talahuhta/PCB-Manufacturing-Project/pictures/3D2.jpg

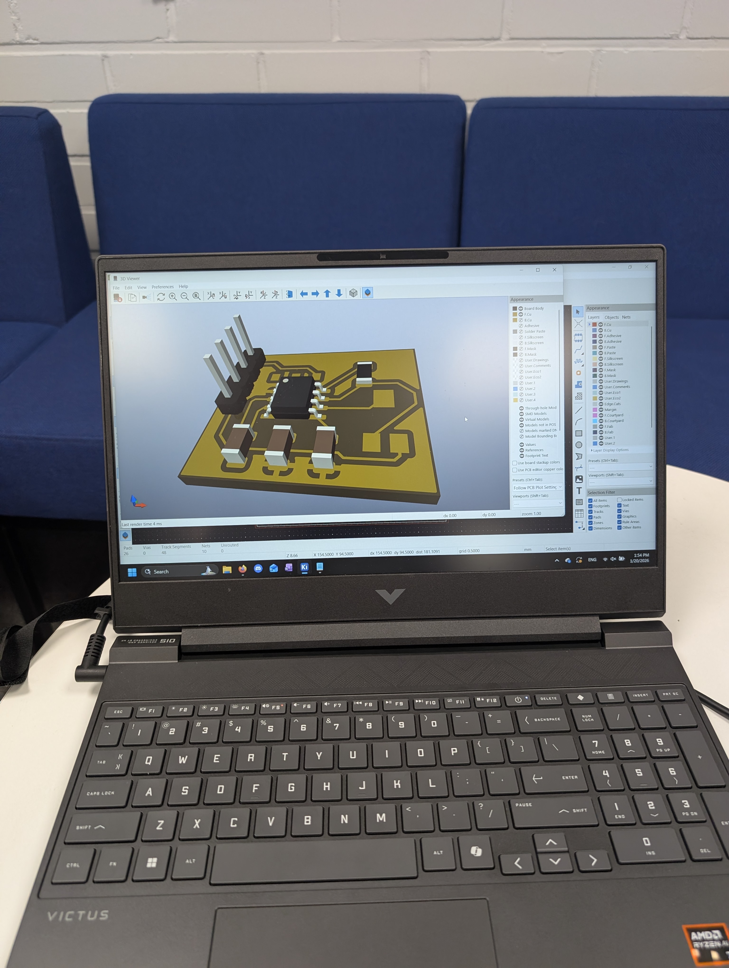
pictures/3D2.jpg
