talahuhta/PCB-Manufacturing-Project/pictures/3D.jpg

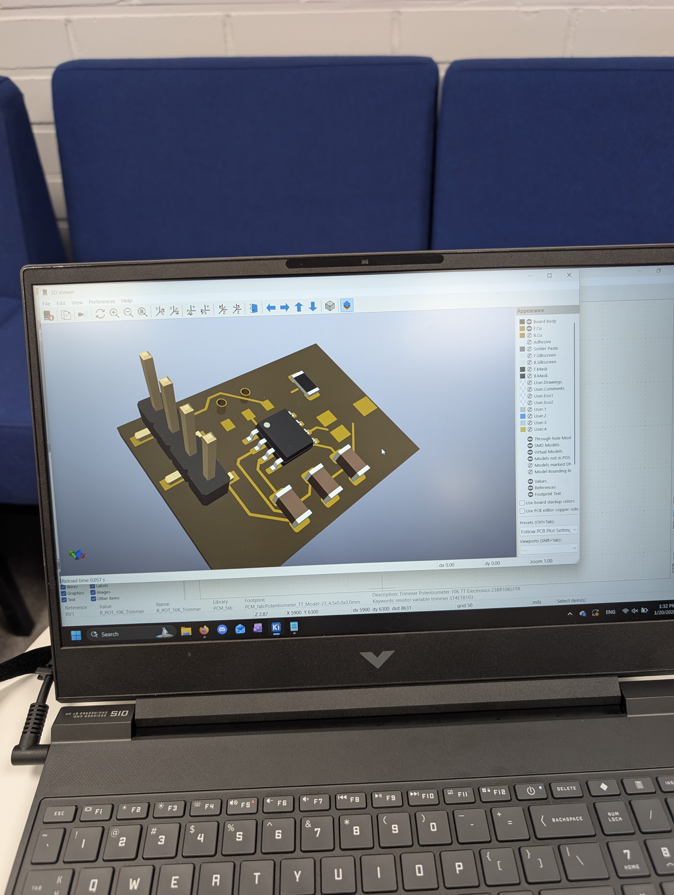
pictures/3D.jpg
