talahuhta/PCB-Manufacturing-Project/pictures/Capacitors.jpg

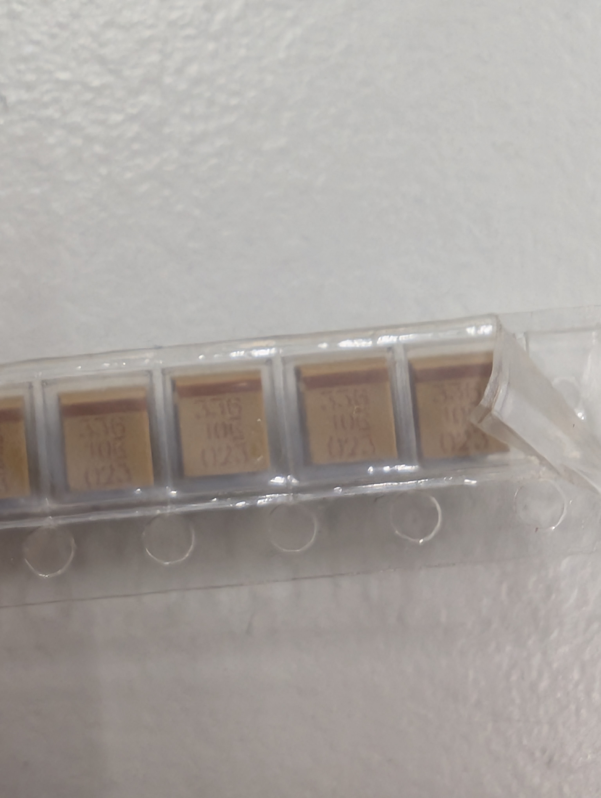
pictures/Capacitors.jpg
