talahuhta/PCB-Manufacturing-Project/pictures/Gerbers.png

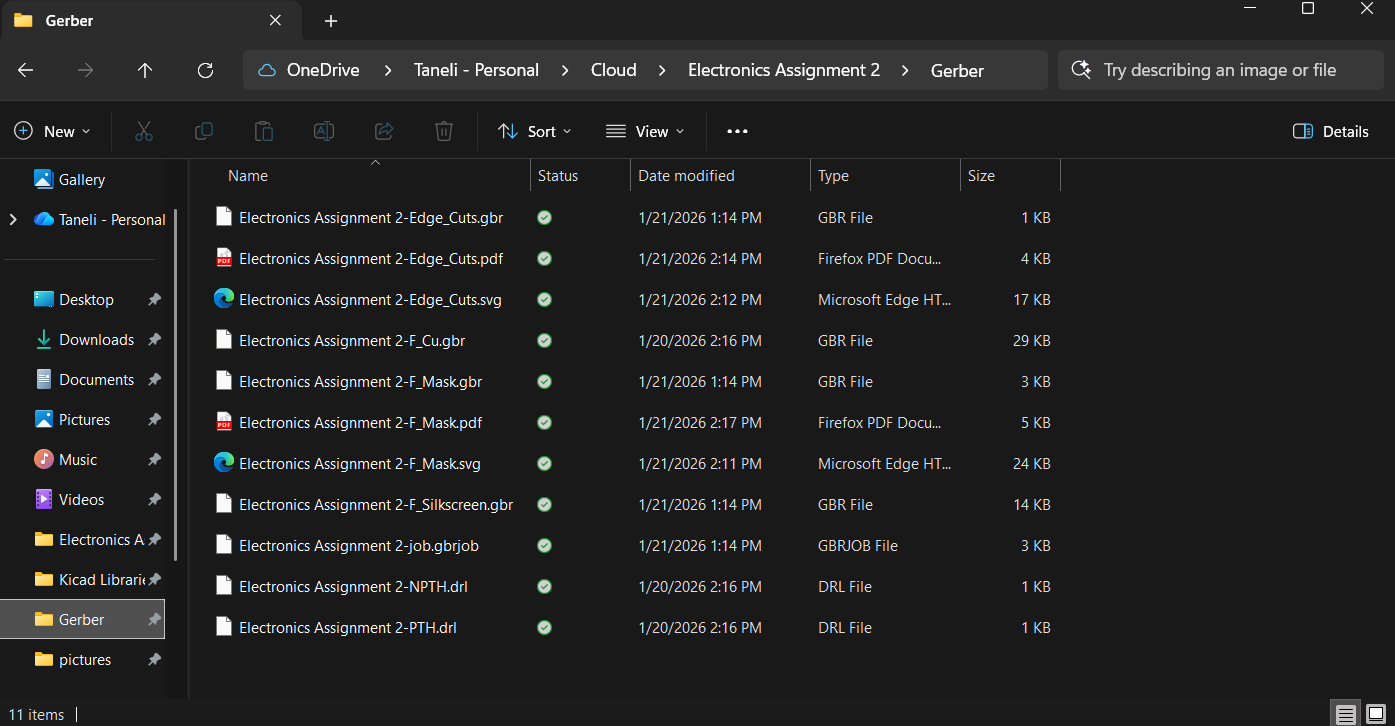
pictures/Gerbers.png
