talahuhta/PCB-Manufacturing-Project/pictures/Inked.jpeg

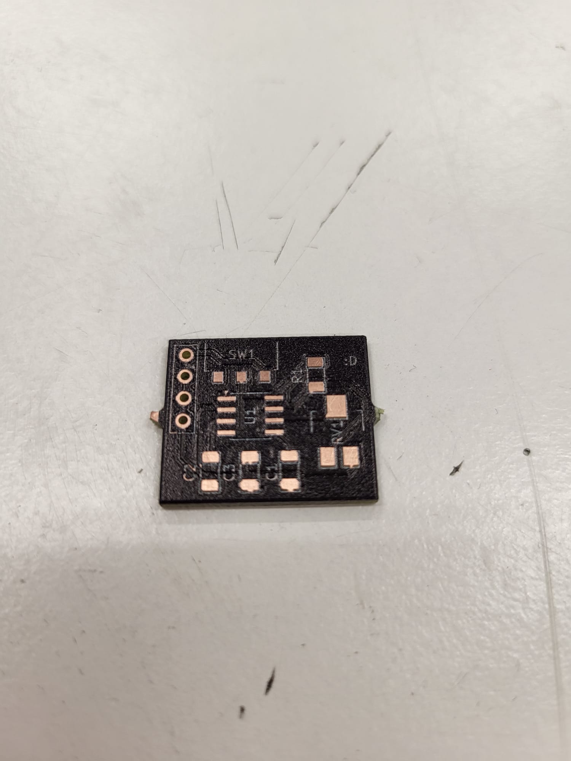
pictures/Inked.jpeg
