talahuhta/PCB-Manufacturing-Project/pictures/InScope.jpg

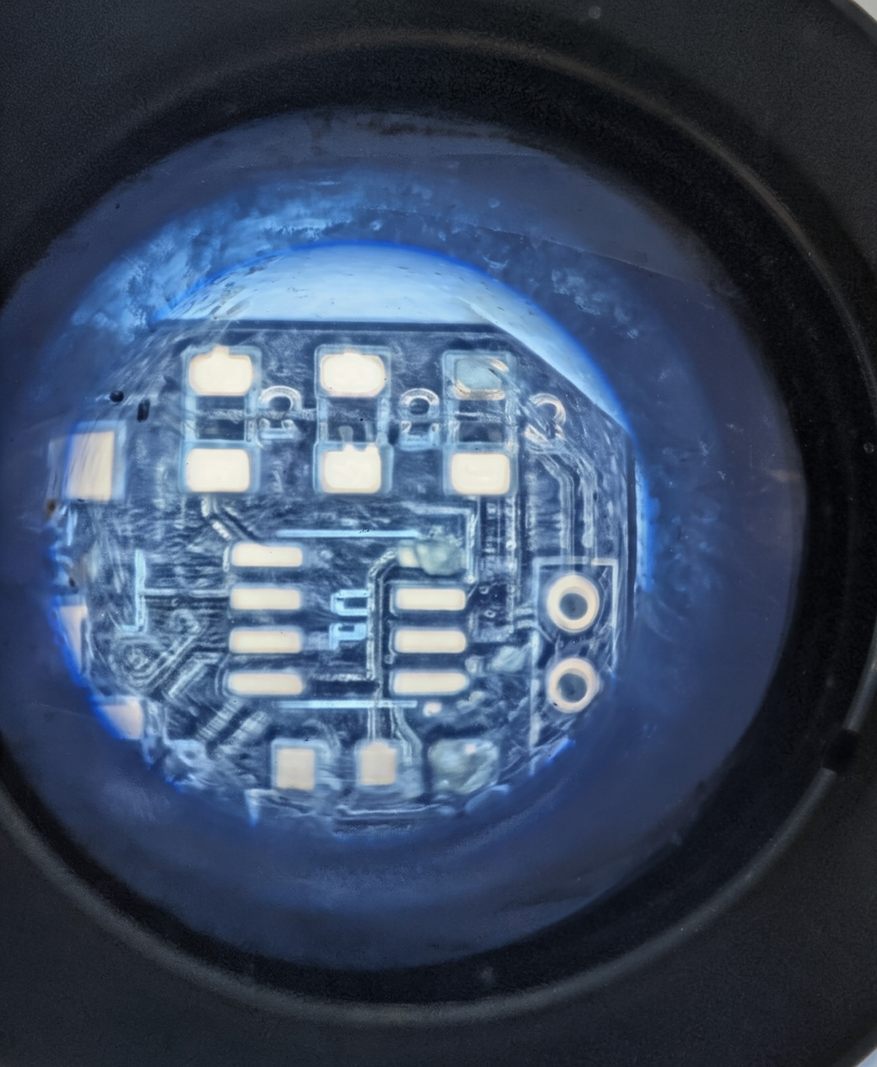
pictures/InScope.jpg
