talahuhta/PCB-Manufacturing-Project/pictures/MicroscopeClose.jpg

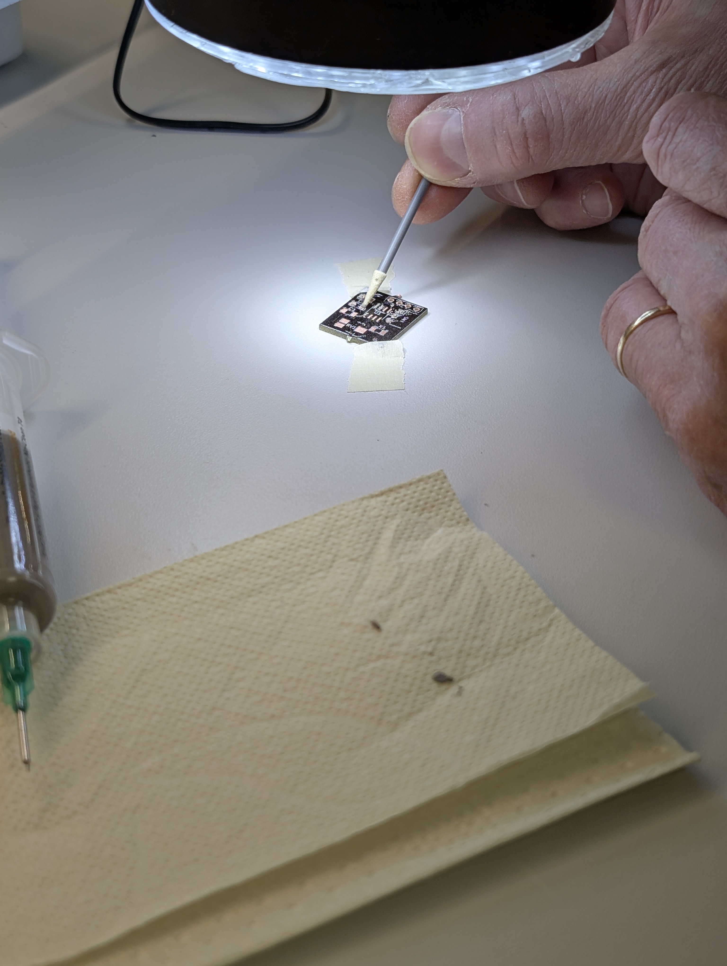
pictures/MicroscopeClose.jpg
