talahuhta/PCB-Manufacturing-Project/pictures/millah.jpeg

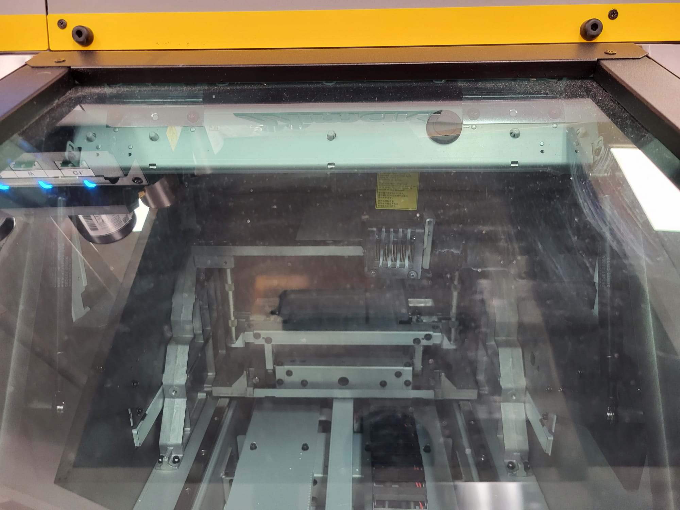
pictures/millah.jpeg
