talahuhta/PCB-Manufacturing-Project/pictures/OvenClose.jpg

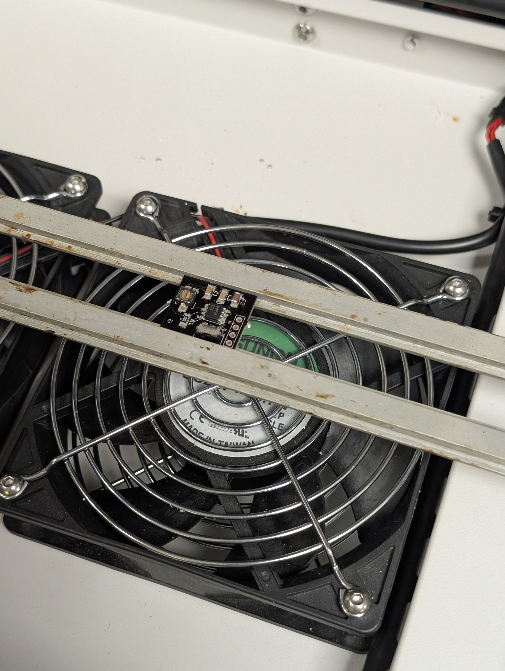
pictures/OvenClose.jpg
