talahuhta/PCB-Manufacturing-Project/pictures/OvenOn.jpg

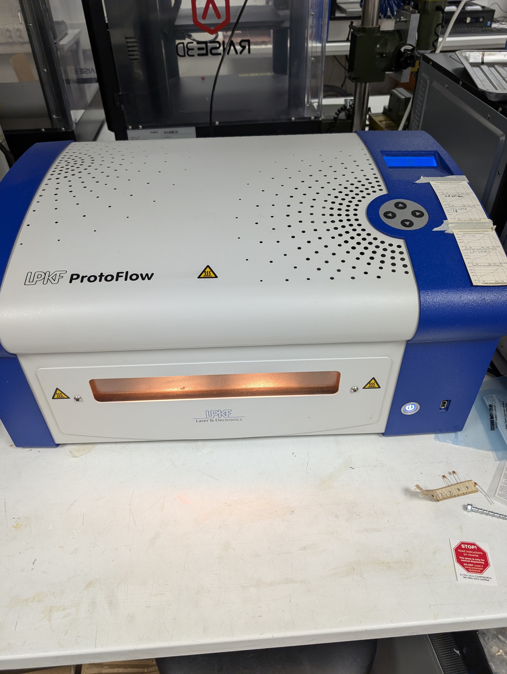
pictures/OvenOn.jpg
