talahuhta/PCB-Manufacturing-Project/pictures/Testing2.jpg

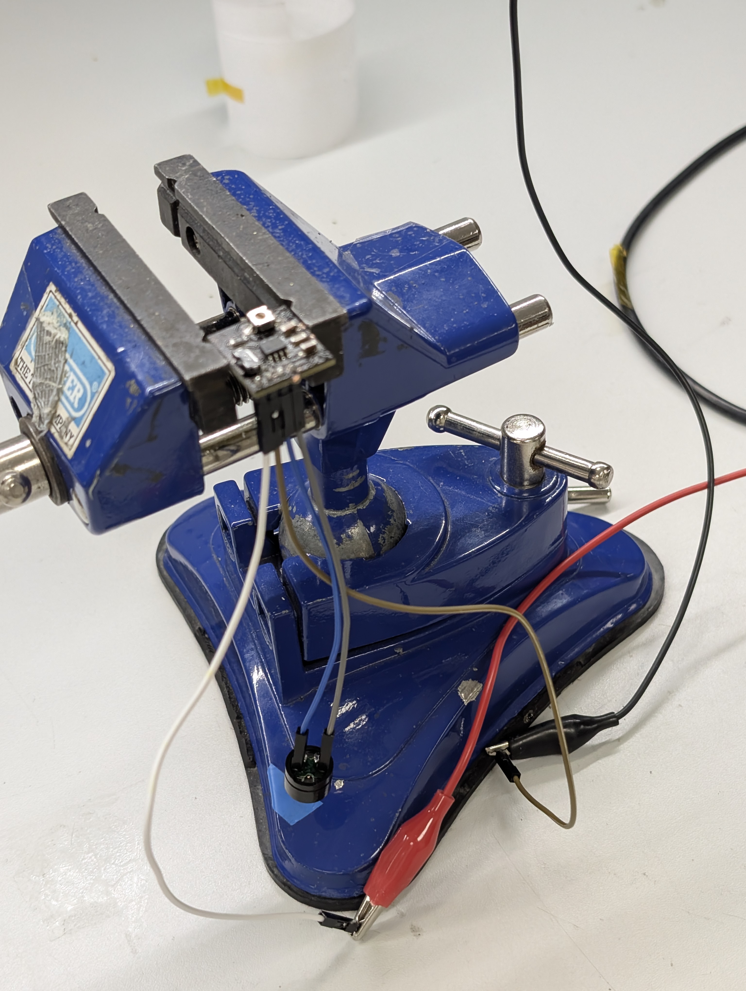
pictures/Testing2.jpg
